mfkiwl/AD4630-Wideband-Digital-LNA/sim/Digital LNA Front End.asc

C1: cap; 1000µF
R1: res; 1.5K
R2: res; 1K
R3: res; 1R
U1: ADA4528-2
V1: voltage; 0V
V2: voltage; 5V
V3: voltage; 5V
V4: voltage; 2.5V
Named nets: 0, +V, -V, out
.noise V(out) V1 dec 100 0.001 1Meg
