mfkiwl/AD4630-Wideband-Digital-LNA/Software/Simulation/Front End.asc

C1: cap; 10m
C2: cap; 10m
R1: res; 330
R2: res; 16K
R3: res; 16K
R4: res; 1
R5: res; 330
R6: res; 1
R7: res; 2K
R8: res; 1K
R9: res; 2K
R10: res; 1K
U1: ADA4528-2
U2: ADA4528-2
U3: LTC6362
V1: voltage; 2.5
V2: voltage; 2.5
V3: voltage; 1; AC 1
V4: voltage; 5
V6: voltage; 2.5V
Named nets: 0, +2.5, -2.5, filterout, +5, ampout, diffout
.ac dec 100 0.01 10k
;noise V(diffout) V3 dec 100 0.01 10k
0.001Hz cutoff RC values:
10mF 16K
This gives ~6nV/rtHz noise down to 10mHz
Additionally down to ~3.5nV/rtHz with 2x fully-diff amp gain
